bilalemregirit/Auto_Announcement/3.5inchnextion_psd/3.5n arkaplan_sefer.png

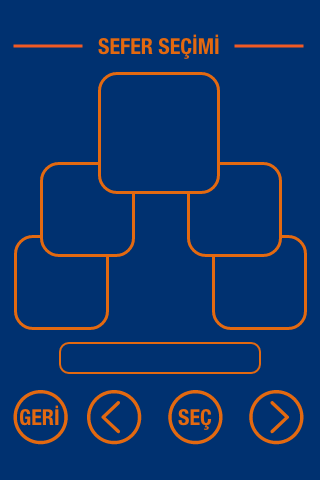
3.5inchnextion_psd/3.5n arkaplan_sefer.png
