bilalemregirit/Auto_Announcement/3.5inchnextion_psd/ANA EKRANsssssssssssssssssssss.png

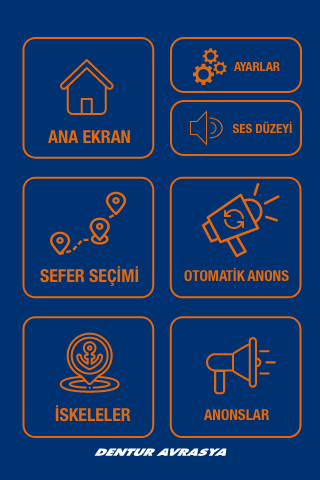
3.5inchnextion_psd/ANA EKRANsssssssssssssssssssss.png
