bilalemregirit/Auto_Announcement/3.5inchnextion_psd/ANONS ANA EKRAN.png

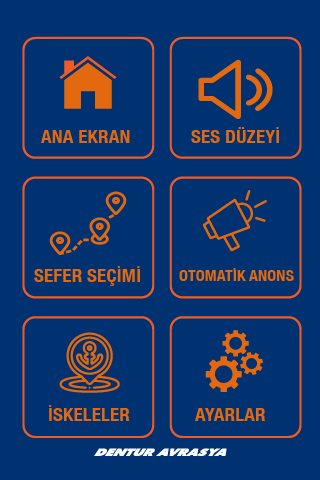
3.5inchnextion_psd/ANONS ANA EKRAN.png
