bilalemregirit/Auto_Announcement/3.5inchnextion_psd/arkaplan_sayf1.png

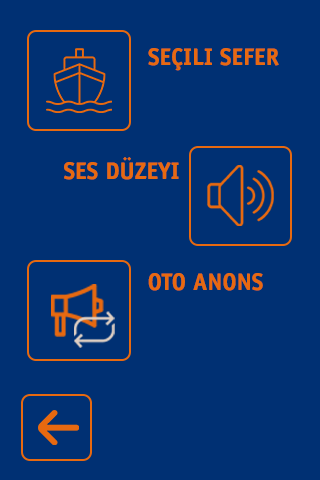
3.5inchnextion_psd/arkaplan_sayf1.png
