bilalemregirit/Auto_Announcement/3.5inchnextion_psd/arkaplanses.png

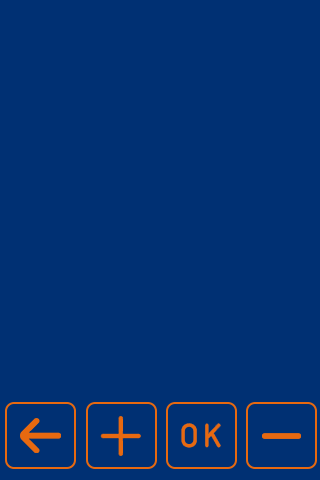
3.5inchnextion_psd/arkaplanses.png
