bilalemregirit/Auto_Announcement/3.5inchnextion_psd/gezii.png

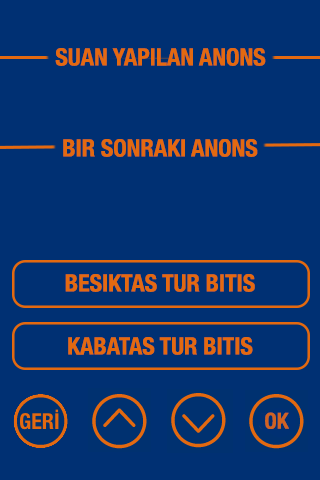
3.5inchnextion_psd/gezii.png
