bilalemregirit/Auto_Announcement/3.5inchnextion_psd/İskeleler.png

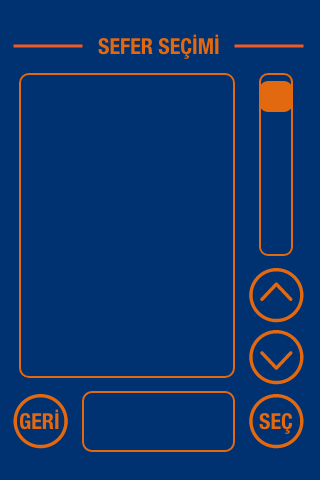
3.5inchnextion_psd/İskeleler.png
