bilalemregirit/Auto_Announcement/3.5inchnextion_psd/kcuksefetr22s.png

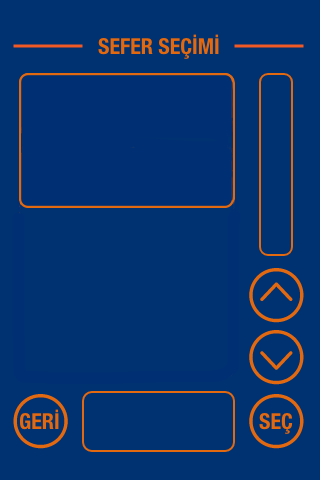
3.5inchnextion_psd/kcuksefetr22s.png
