bilalemregirit/Auto_Announcement/3.5inchnextion_psd/otomatik anons.png

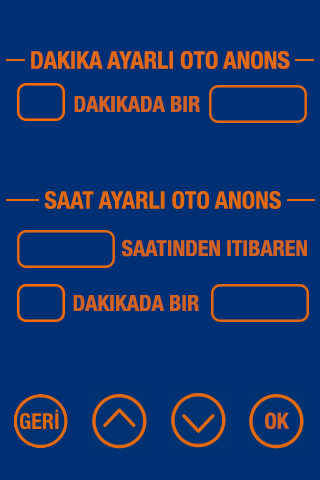
3.5inchnextion_psd/otomatik anons.png
