bilalemregirit/Auto_Announcement/3.5inchnextion_psd/uyarıanons.png

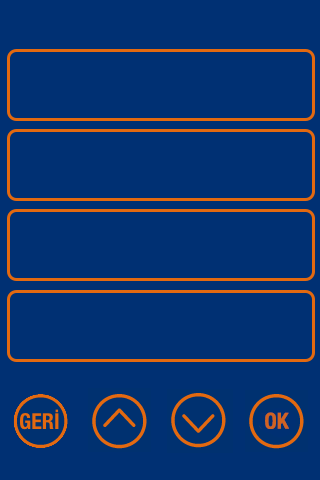
3.5inchnextion_psd/uyarıanons.png
